QBioLab/let-there-be-light/Mechanism/BGC串口协议/491897285214955919.png

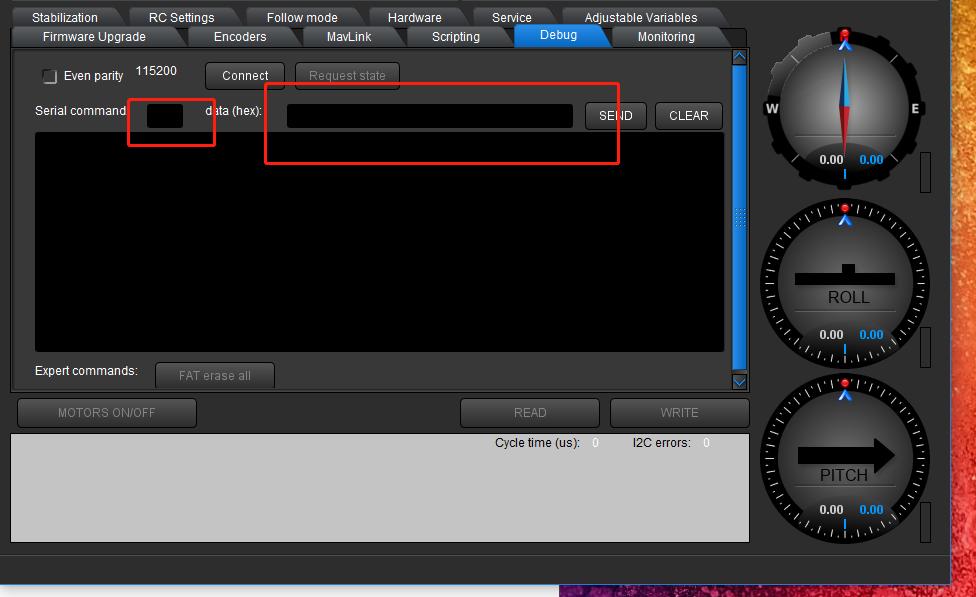
Mechanism/BGC串口协议/491897285214955919.png
