QBioLab/let-there-be-light/Mechanism/BGC串口协议/891594542949472046.png

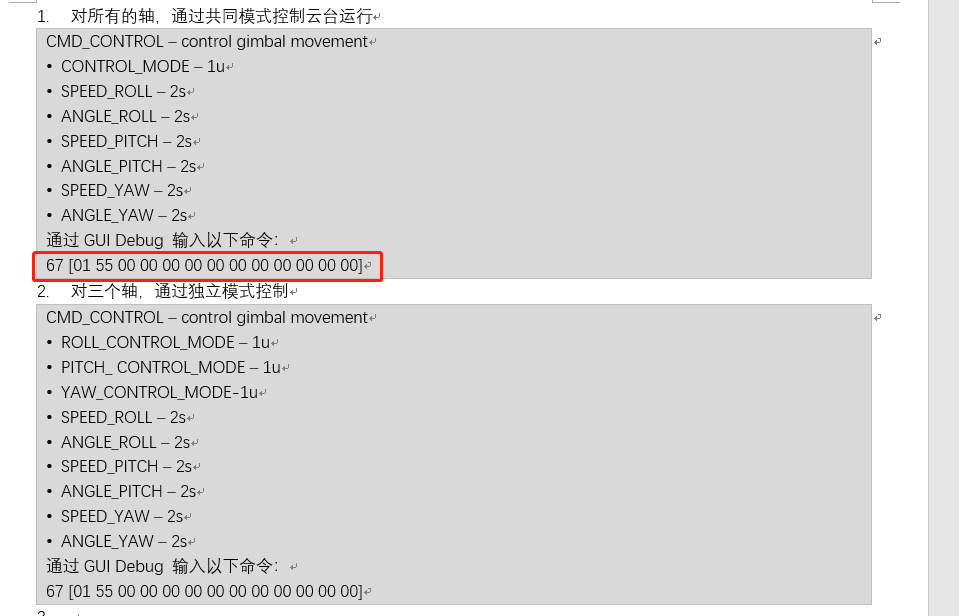
Mechanism/BGC串口协议/891594542949472046.png
