QBioLab/let-there-be-light/Mechanism/CNC/gimbal-gun2-攻丝标注-20210416.png

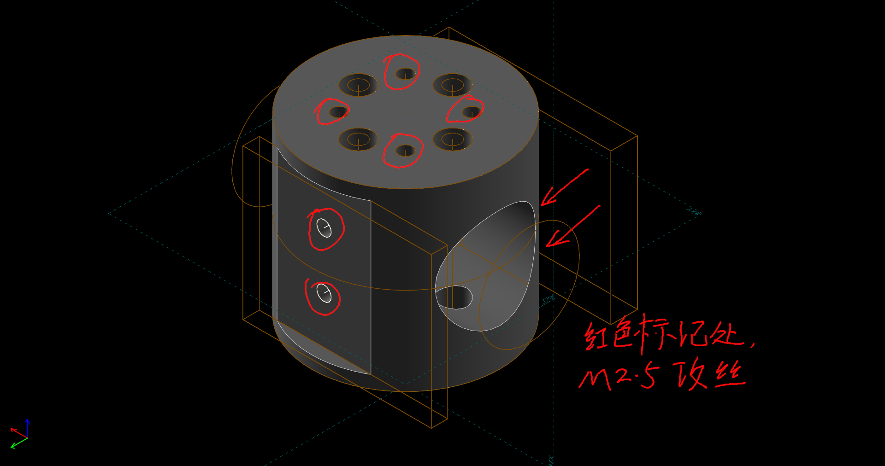
Mechanism/CNC/gimbal-gun2-攻丝标注-20210416.png
