QBioLab/let-there-be-light/Mechanism/CNC/gimbal-header2.step

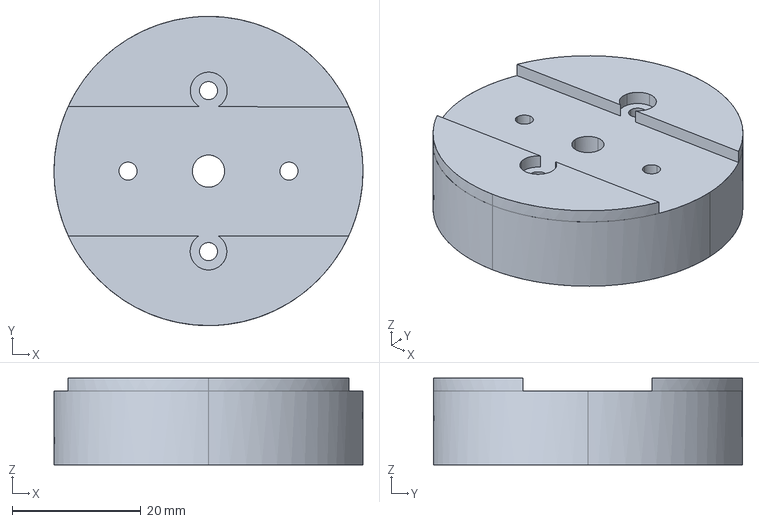
[picture p22: CAD file, 2021-04-08]
Mechanism/CNC/gimbal-header2.step
48.0 x 48.0 x 13.5 mm
